climent/SouffleKeyboard/docs/images/souffle_vr_encoder_side_view.jpg

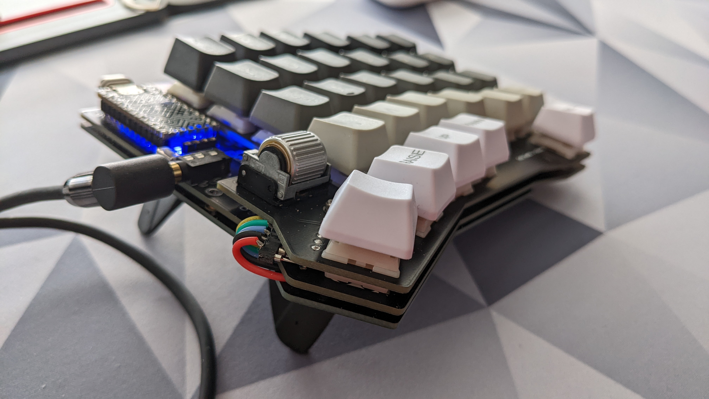
docs/images/souffle_vr_encoder_side_view.jpg
