climent/SouffleKeyboard/docs/images/souffle_vr_encoder_top_view_1.jpg

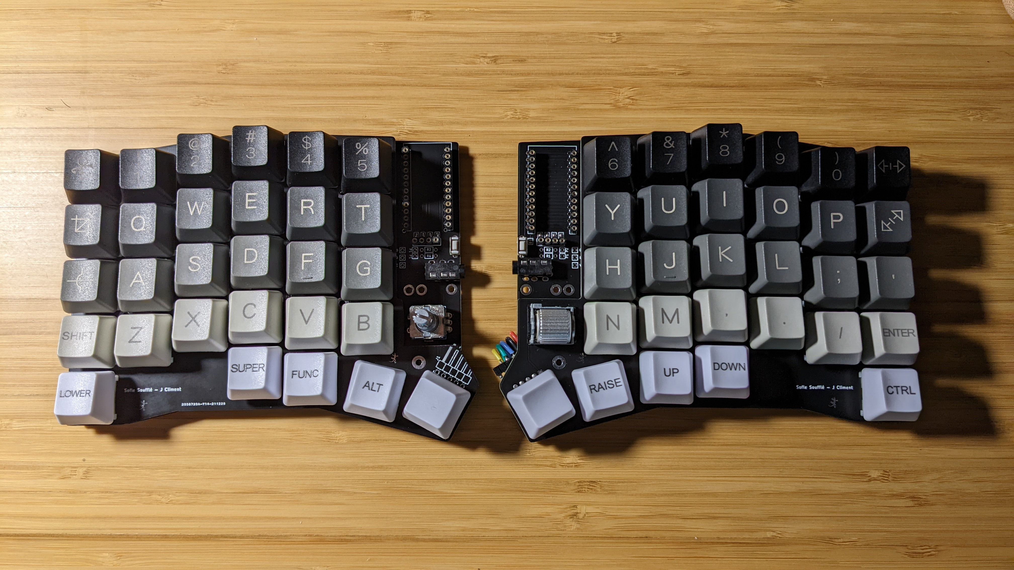
docs/images/souffle_vr_encoder_top_view_1.jpg
