climent/SouffleKeyboard/docs/images/SouffleKeyboard_v2_gerber_view_bottom.png

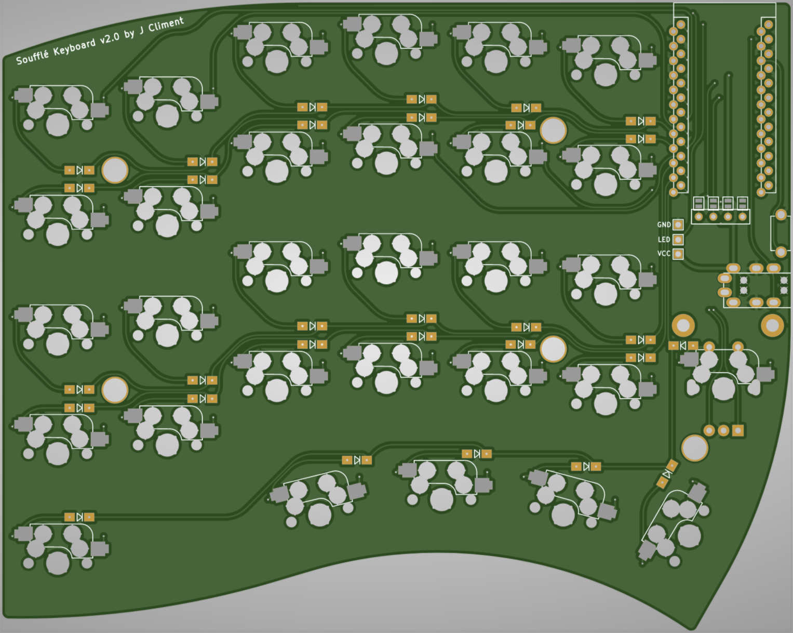
docs/images/SouffleKeyboard_v2_gerber_view_bottom.png
