climent/SouffleKeyboard/docs/images/SouffleKeyboard_v2_gerber_view_layers.png

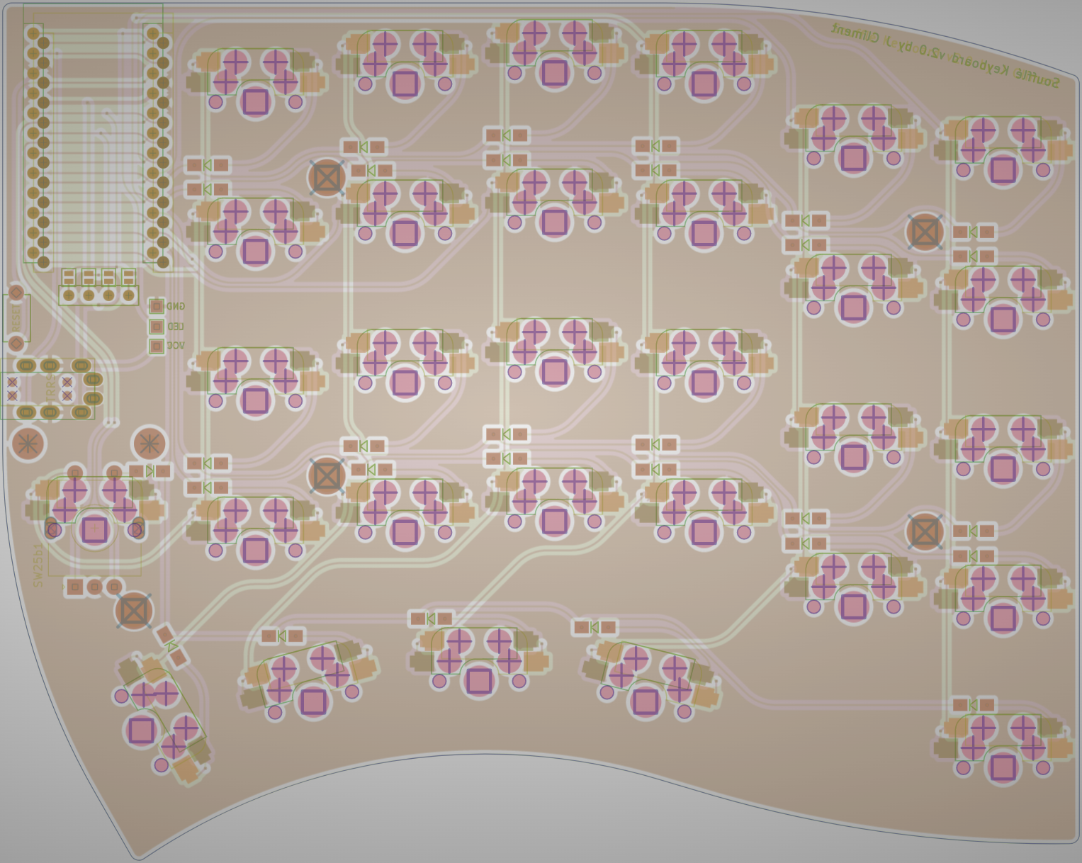
docs/images/SouffleKeyboard_v2_gerber_view_layers.png
