climent/SouffleKeyboard/docs/images/SouffleKeyboard_v2_gerber_view_top.png

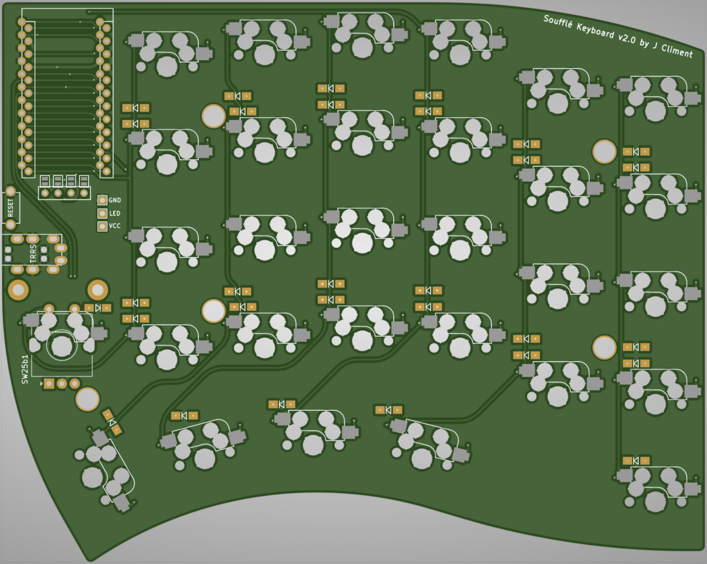
docs/images/SouffleKeyboard_v2_gerber_view_top.png
