climent/SouffleKeyboard/docs/images/SouffleKeyboard_v2_PCB_KiCad.png

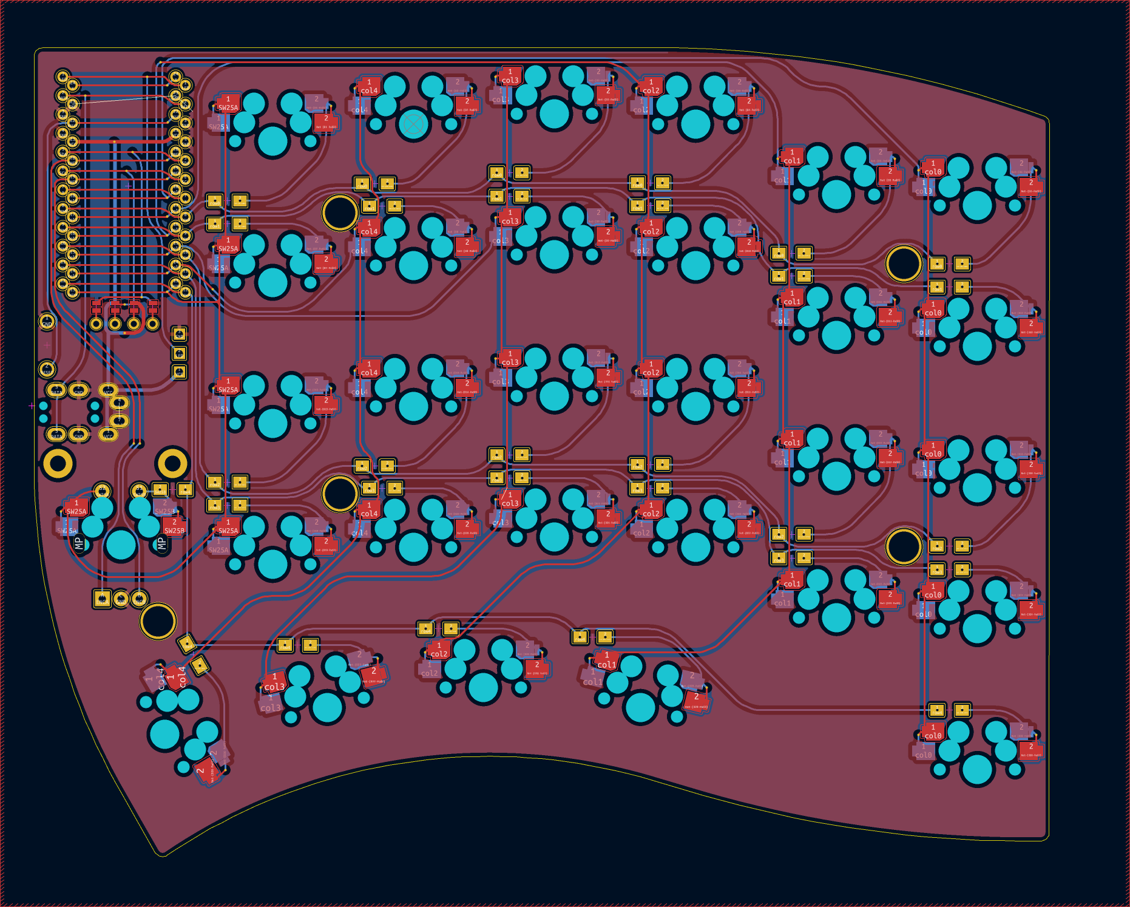
docs/images/SouffleKeyboard_v2_PCB_KiCad.png
