climent/SouffleKeyboard/docs/images/build_guide/PXL_20220824_180313825.jpg

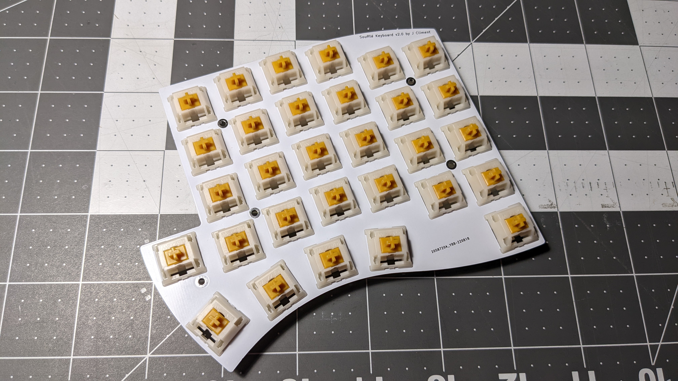
docs/images/build_guide/PXL_20220824_180313825.jpg
