climent/SouffleKeyboard/docs/images/build_guide/PXL_20220824_180635226.jpg

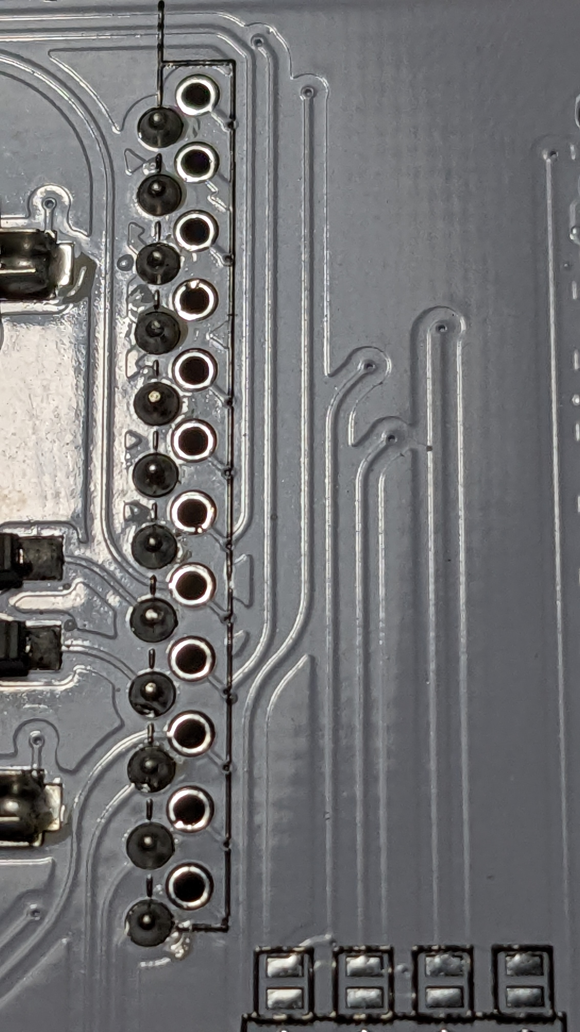
docs/images/build_guide/PXL_20220824_180635226.jpg
