climent/SouffleKeyboard/docs/images/build_guide/PXL_20220824_180639597.jpg

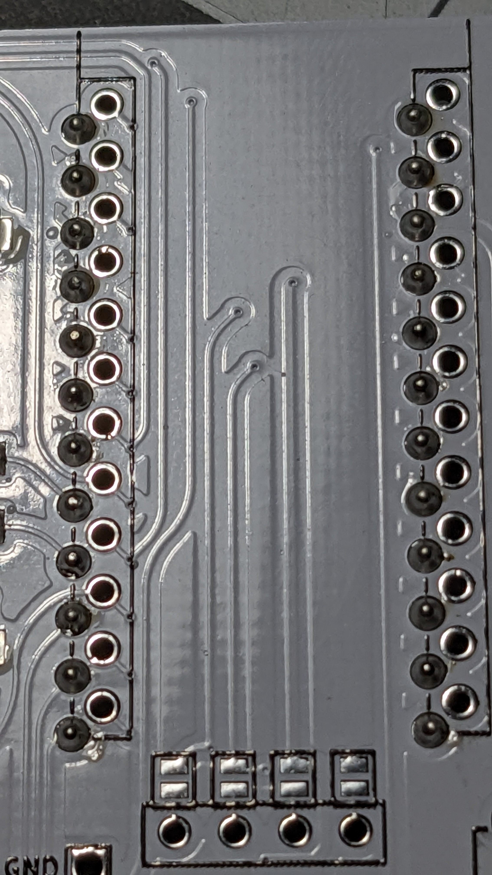
docs/images/build_guide/PXL_20220824_180639597.jpg
