climent/SouffleKeyboard/docs/images/build_guide/PXL_20220824_180703349.jpg

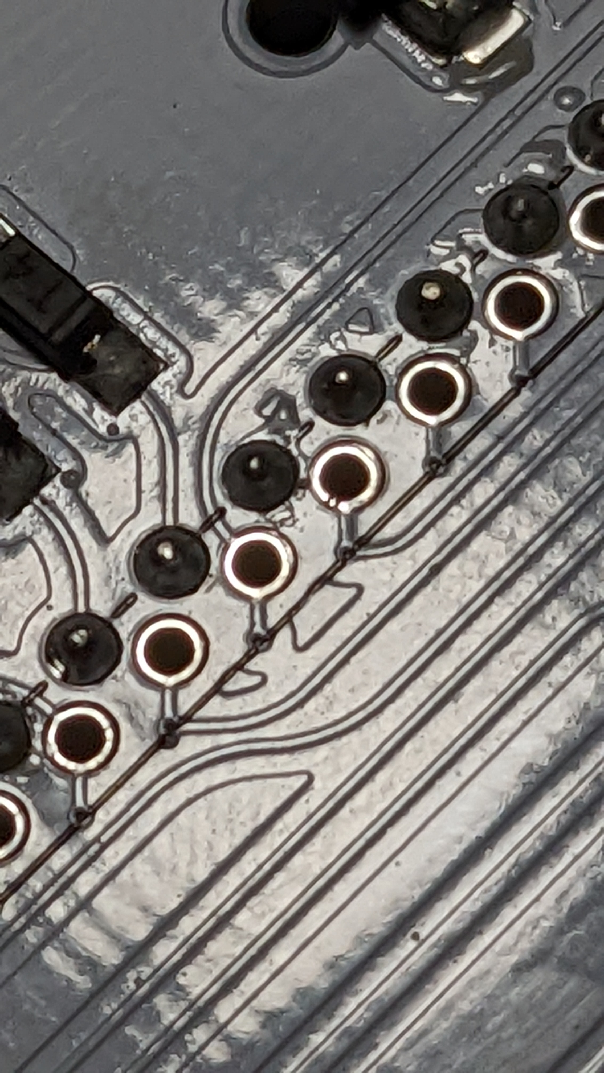
docs/images/build_guide/PXL_20220824_180703349.jpg
