climent/SouffleKeyboard/docs/images/build_guide/PXL_20220824_180728764.jpg

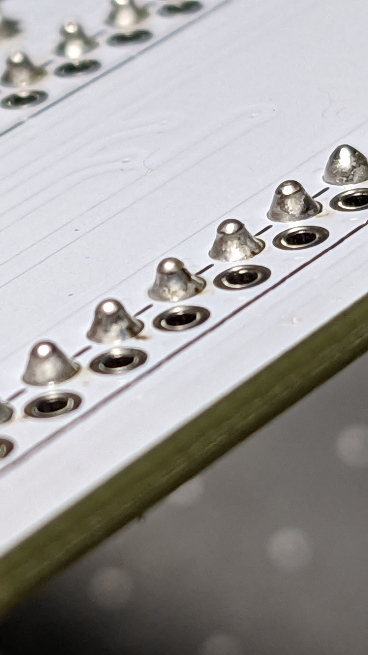
docs/images/build_guide/PXL_20220824_180728764.jpg
