climent/SouffleKeyboard/docs/images/build_guide/PXL_20220824_181402377.MP.jpg

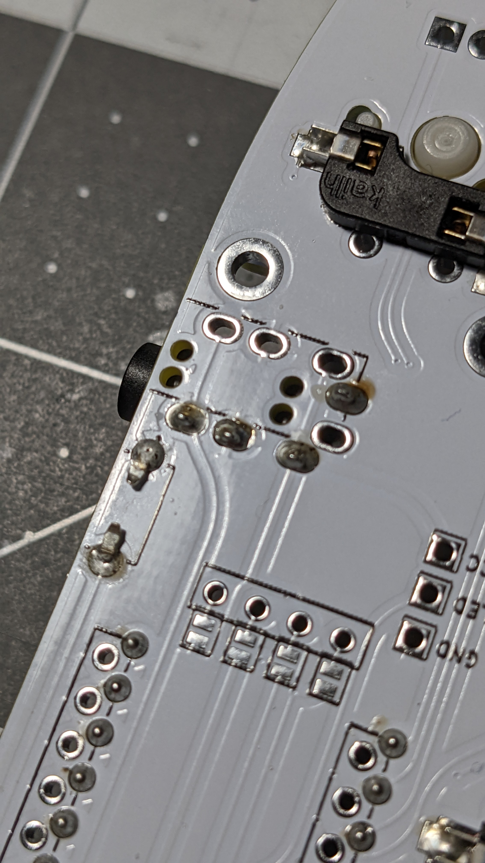
docs/images/build_guide/PXL_20220824_181402377.MP.jpg
