climent/SouffleKeyboard/docs/images/build_guide/PXL_20220824_181412347.jpg

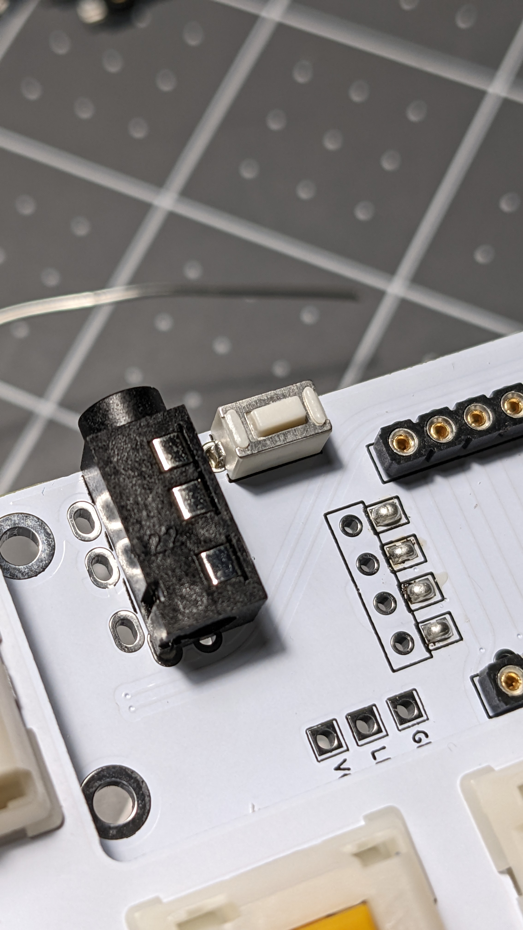
docs/images/build_guide/PXL_20220824_181412347.jpg
