climent/SouffleKeyboard/docs/images/build_guide/PXL_20220824_182104894.jpg

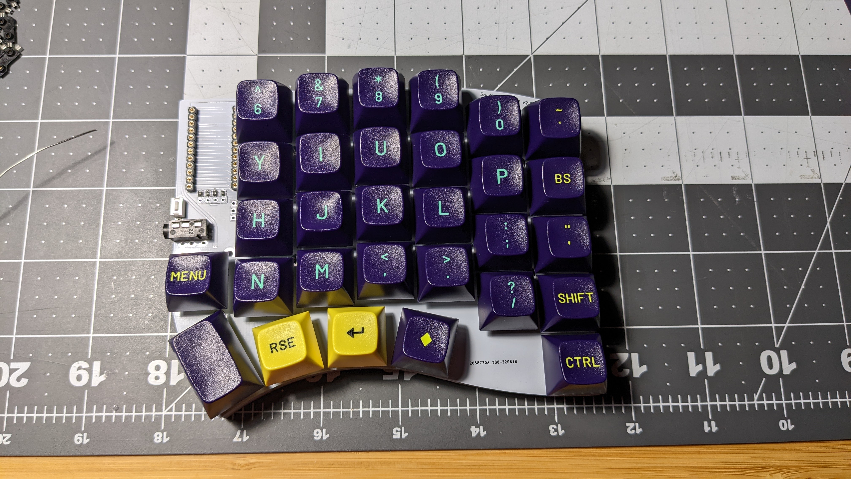
docs/images/build_guide/PXL_20220824_182104894.jpg
