climent/SouffleKeyboard/docs/images/build_guide/PXL_20230415_152200340.jpg

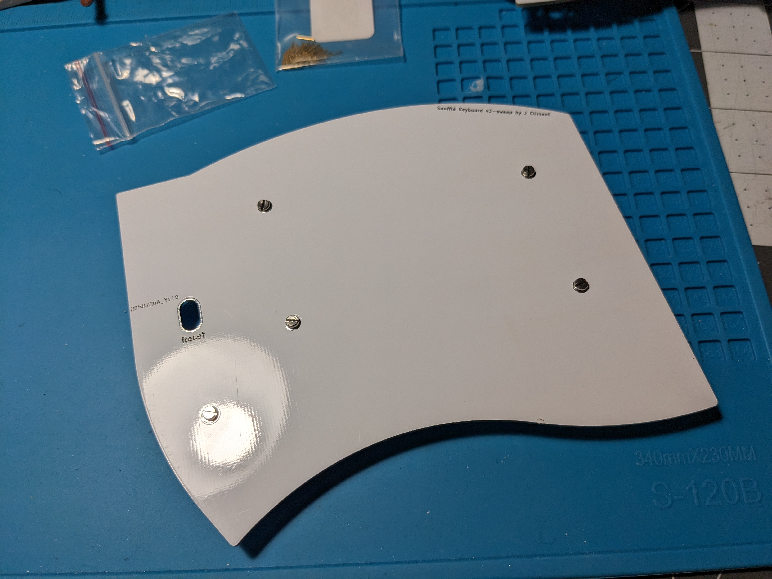
docs/images/build_guide/PXL_20230415_152200340.jpg
