climent/SouffleKeyboard/docs/images/build_guide/PXL_20230415_152533738.jpg

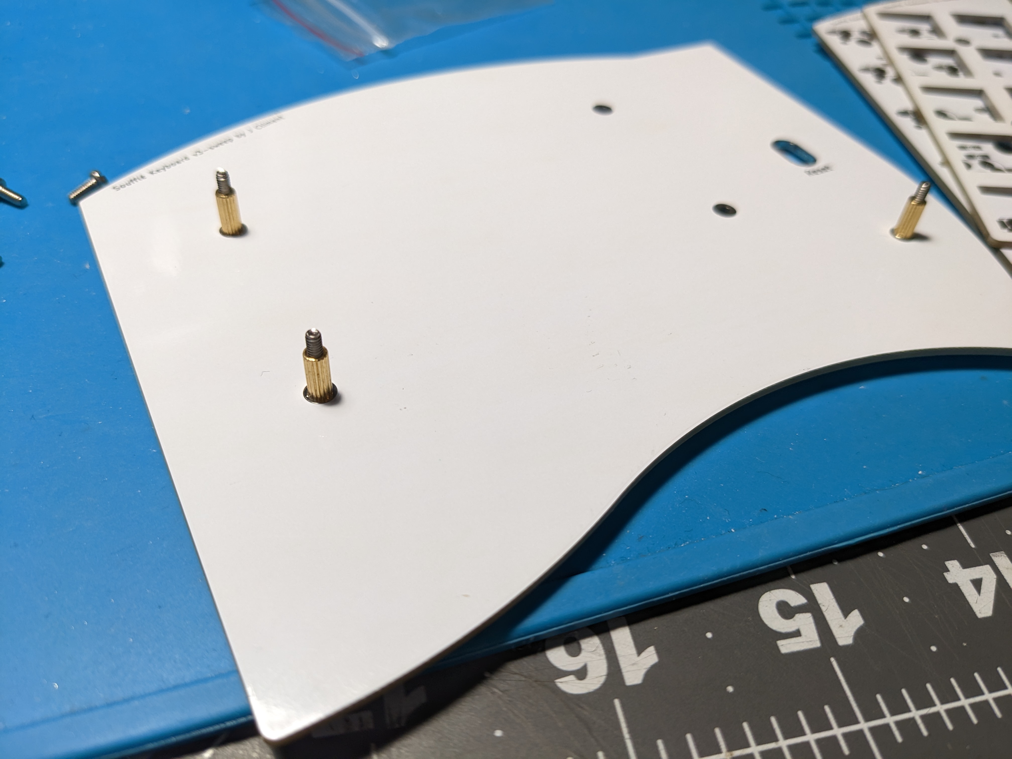
docs/images/build_guide/PXL_20230415_152533738.jpg
