climent/SouffleKeyboard/docs/images/build_guide/PXL_20230415_152637402.jpg

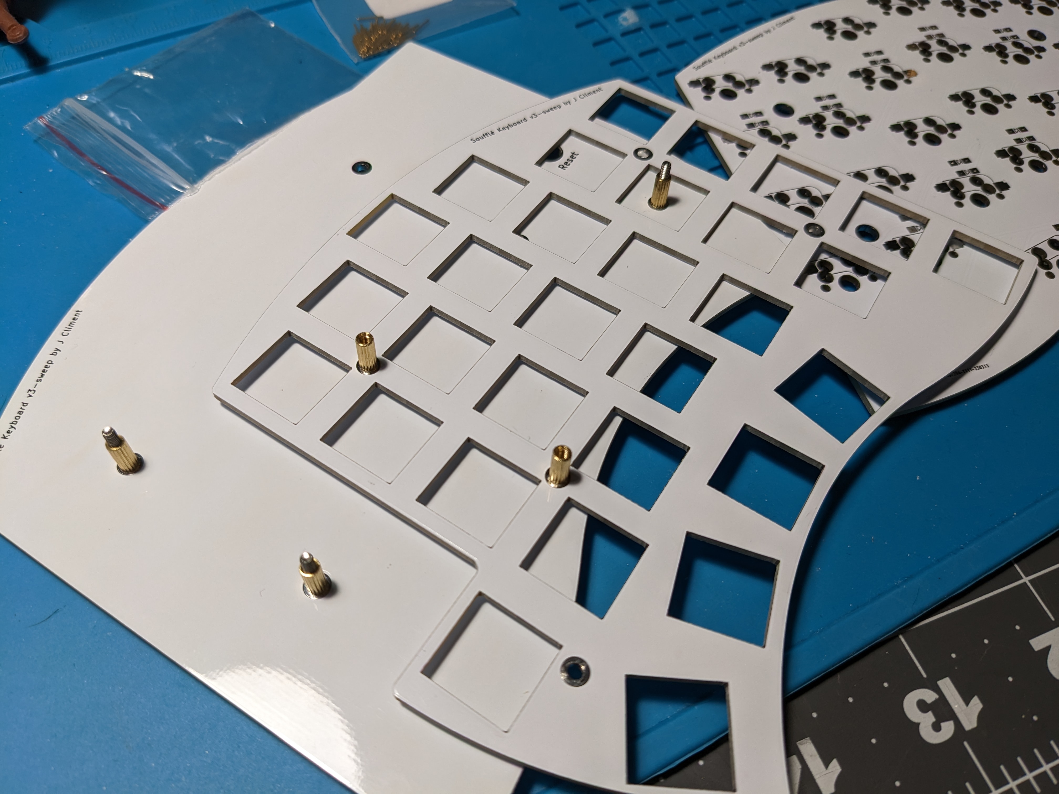
docs/images/build_guide/PXL_20230415_152637402.jpg
